tkottke90/racing_control_panel/STL/Part Concept-StreamDeck Panel Bottom.stl

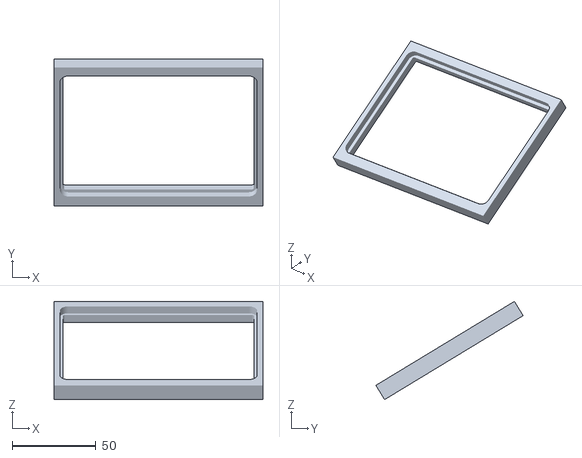
[picture p17: CAD file, 2023-11-17]
STL/Part Concept-StreamDeck Panel Bottom.stl
125.1 x 88.1 x 58.8
