tkottke90/racing_control_panel/STL/StreamDeck_Cover.stl

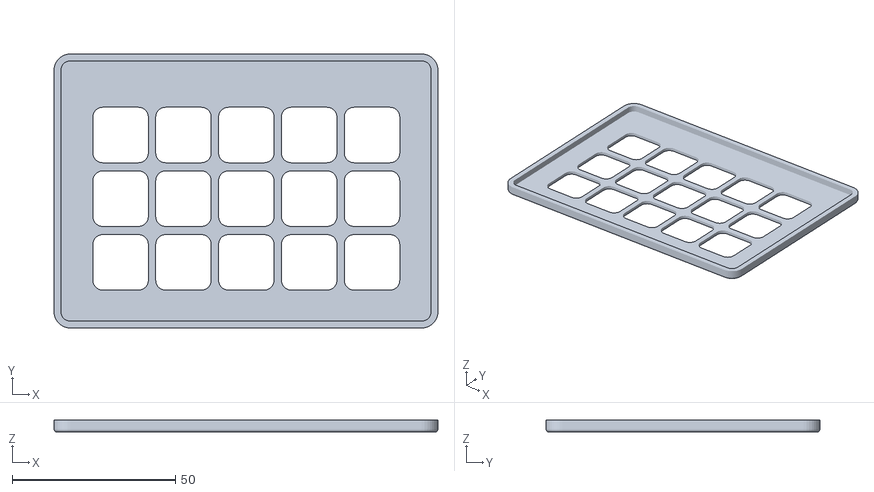
[picture p18: CAD file, 2023-11-17]
STL/StreamDeck_Cover.stl
117.6 x 83.9 x 3.80
